HonestLocksmith/piglet/Arduino Files/Piglet/SDUtils.h

#pragma once
#include <Arduino.h>

bool   openLogFile();
void   closeLogFile();
void   appendWigleRow(const String& mac, const String& ssid, const String& auth,
                      const String& firstSeen, int channel, int rssi,
                      double lat, double lon, double altM, double accM);

String normalizeSdPath(const char* dir, const char* nameIn);
String pathBasename(const String& p);
bool   isAllowedDataPath(const String& p);
bool   moveToUploaded(const String& srcPath);
